Te55er4ct/phi-harmonic-toroidal-field/sessions/2026-06-06_session1_v1/V1_1MHz_1.2MHz_SRF.png

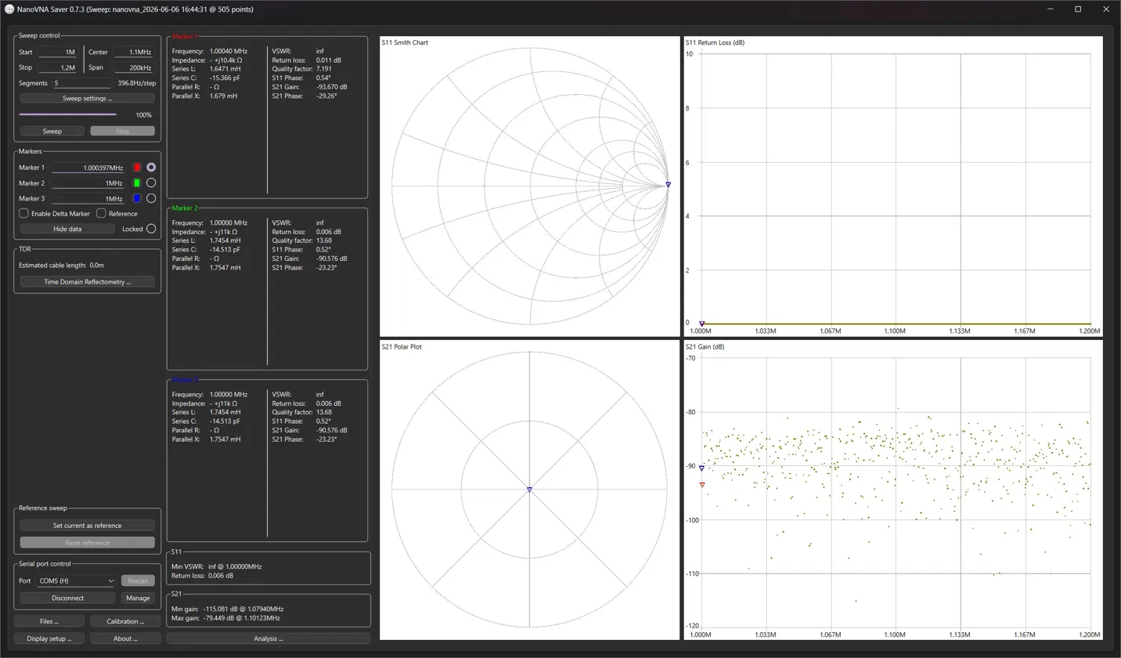
sessions/2026-06-06_session1_v1/V1_1MHz_1.2MHz_SRF.png
