Te55er4ct/phi-harmonic-toroidal-field/sessions/2026-06-06_session1_v1/v1_glue_cure.png

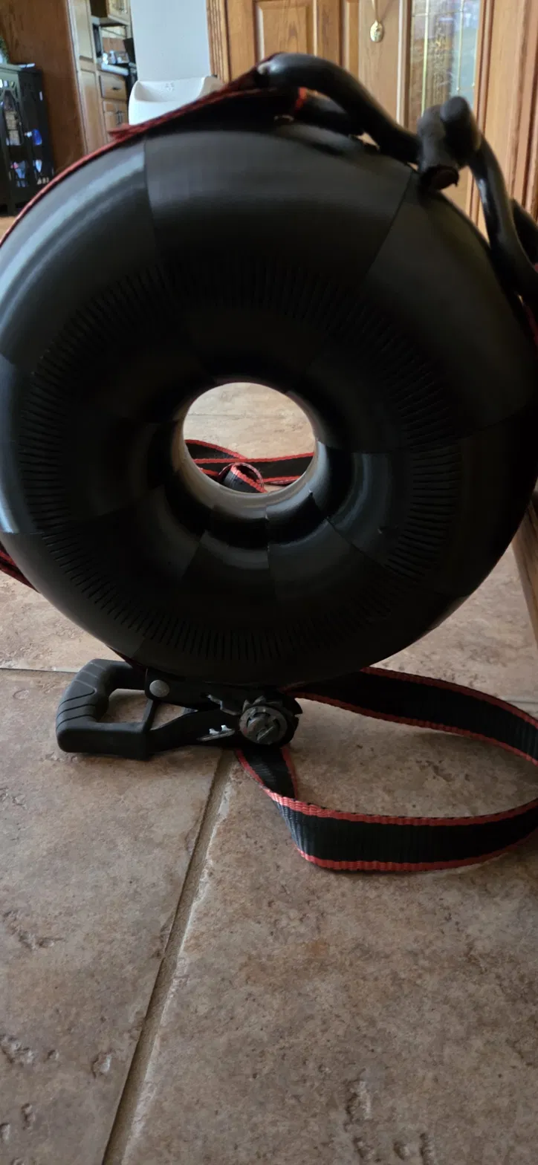
sessions/2026-06-06_session1_v1/v1_glue_cure.png
